printsmith/N64Portable/cad/stl/Top_Case/Top_Shell.stl

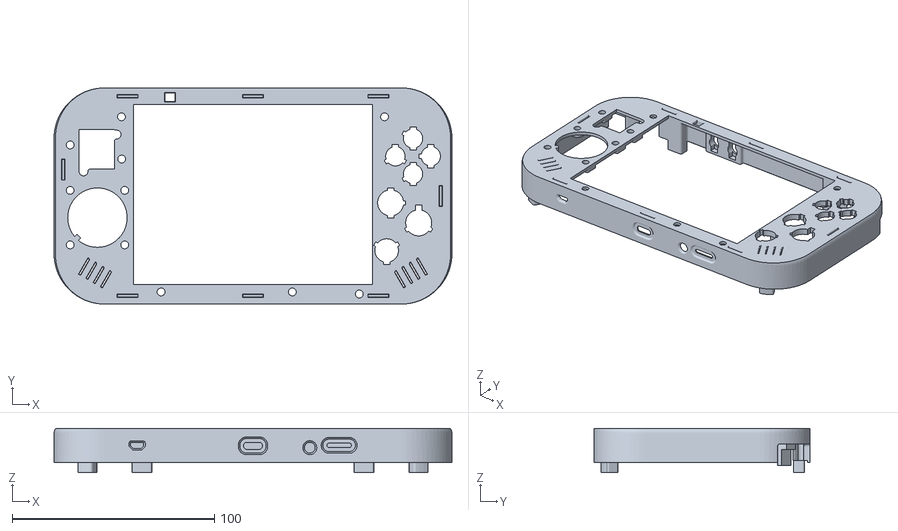
[picture p24: CAD file, 2021-06-14]
cad/stl/Top_Case/Top_Shell.stl
197.0 x 107.0 x 21.8
