printsmith/N64Portable/cad/stl/Bottom_Case/Cartridge_Cover.stl

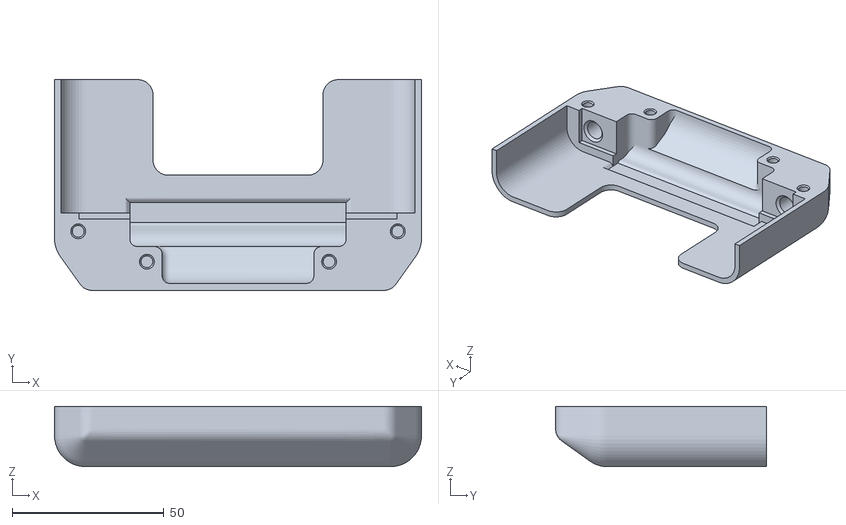
[picture p25: CAD file, 2021-06-14]
cad/stl/Bottom_Case/Cartridge_Cover.stl
120.9 x 69.5 x 19.9
