printsmith/N64Portable/cad/stl/Internals/Screen_Mount.stl

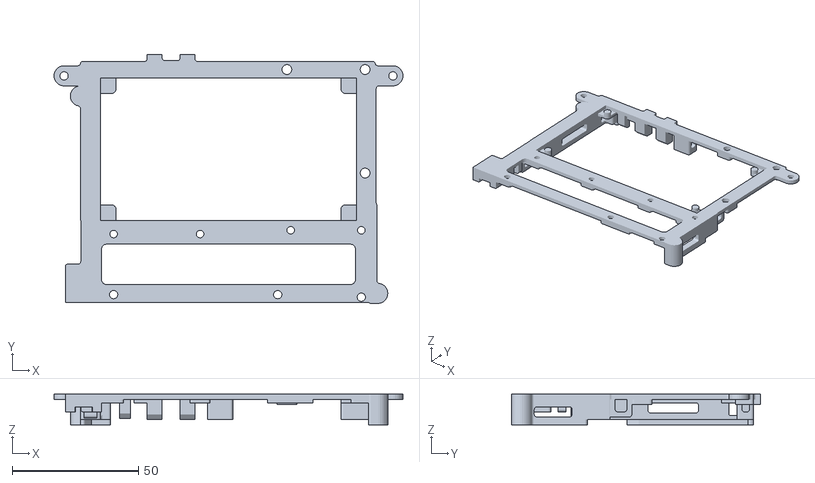
[picture p26: CAD file, 2021-06-14]
cad/stl/Internals/Screen_Mount.stl
138.2 x 98.6 x 12.1
