printsmith/N64Portable/cad/stl/Buttons/ZL_Trigger.stl

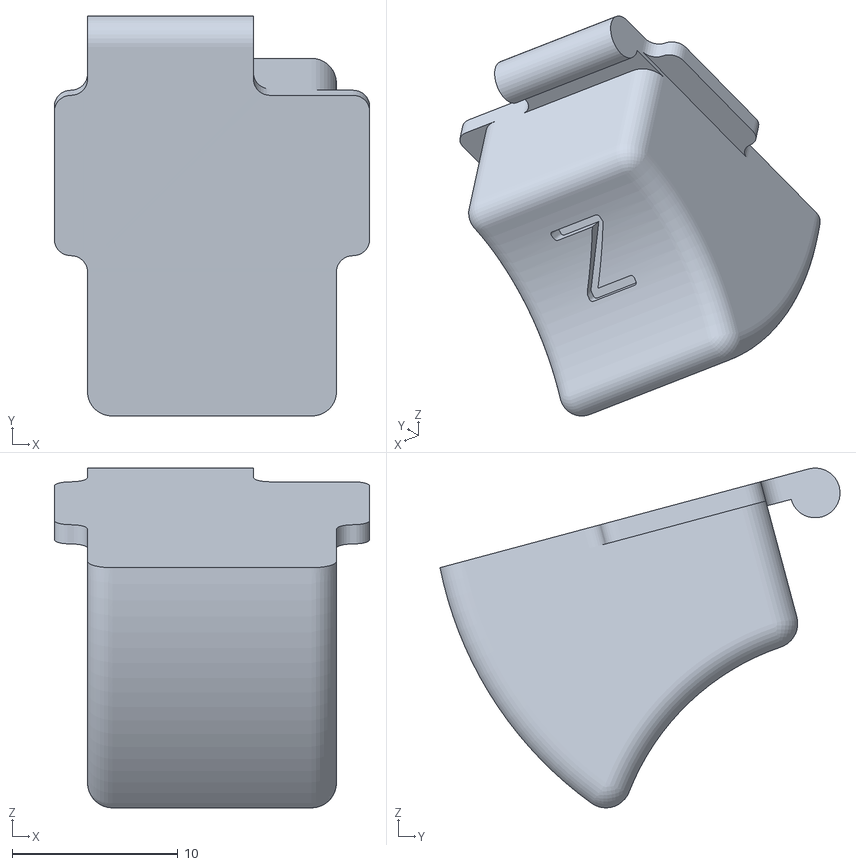
[picture p27: CAD file, 2021-06-14]
cad/stl/Buttons/ZL_Trigger.stl
19.0 x 24.1 x 20.5
